onelenyk/agentlight/firmware/src/api.cpp

// Веб-сервер: сторінка лампи і REST. Опис запитів — у docs/firmware.md.
#include <WiFi.h>
#include "app.h"
#include <uri/UriBraces.h>
#include "assets.h"

WebServer server(80);

void sendJson(int code, const JsonDocument& doc) {
  String out;
  serializeJson(doc, out);
  server.send(code, "application/json", out);
}

static void sendError(int code, const char* text) {
  JsonDocument doc;
  doc["error"] = text;
  sendJson(code, doc);
}

static void restartSoon() {
  server.send(200, "application/json", "{\"ok\":true}");
  delay(500);
  ESP.restart();
}

void fillStatus(JsonObject o) {
  o["state"] = STATE_NAMES[aggregate()];
  fillAgents(o["agents"].to<JsonArray>());
  o["brightness"] = brightness;
  o["mode"] = MODE_NAMES[cfg.mode];
  o["off"] = lightOff;
  o["lamp_left"] = lampSecondsLeft();
  o["sleep_left"] = sleepSecondsLeft();
  fillFocus(o["focus"].to<JsonObject>());
  fillGame(o["play"].to<JsonObject>());
  fillAllow(o["allow"].to<JsonObject>());
  fillRemote(o["remote"].to<JsonObject>());          // пульт: спаровані пристрої і хто з них активний
  JsonObject sig = o["signal"].to<JsonObject>();     // дія сенсора «сигнал агентові»
  sig["count"] = signalCount;
  if (signalCount) sig["ago"] = (millis() - signalAt) / 1000;
  fillWifi(o["wifi"].to<JsonObject>());
}

static const char* resetReason() {
  switch (esp_reset_reason()) {
    case ESP_RST_POWERON:  return "увімкнення живлення";
    case ESP_RST_SW:       return "програмний перезапуск";
    case ESP_RST_PANIC:    return "збій прошивки";
    case ESP_RST_INT_WDT:
    case ESP_RST_TASK_WDT:
    case ESP_RST_WDT:      return "сторожовий таймер";
    case ESP_RST_BROWNOUT: return "просідання живлення";
    default:               return "інше";
  }
}

static String hexColor(uint32_t c) {
  char hex[8];
  snprintf(hex, sizeof hex, "#%06x", (unsigned)(c & 0xFFFFFF));
  return hex;
}

static bool parseColor(const char* hex, uint32_t& out) {
  if (strlen(hex) != 7 || hex[0] != '#') return false;
  out = strtoul(hex + 1, nullptr, 16);
  return true;
}

static void fillDebug(JsonObject o) {
  JsonObject d = o["device"].to<JsonObject>();
  d["version"] = FW_VERSION;
  d["build"] = __DATE__ " " __TIME__;
  d["uptime"] = millis() / 1000;
  d["reset"] = resetReason();
  d["chip"] = ESP.getChipModel();
  d["mac"] = WiFi.macAddress();
  d["heap"] = ESP.getFreeHeap();
  d["heap_min"] = ESP.getMinFreeHeap();
  d["led_pin"] = LED_PIN;
  d["led_max"] = LED_COUNT;
  d["touch_pin"] = TOUCH_PIN;
  d["ota_ready"] = otaReady();
  JsonObject t = o["touch"].to<JsonObject>();
  t["raw"] = touchRaw;
  t["count"] = touchCount;
  if (touchCount) t["ago"] = (millis() - touchAt) / 1000;
  JsonObject c = o["settings"].to<JsonObject>();
  c["brightness"] = brightness;
  c["leds"] = cfg.leds;
  c["ttl_busy"] = cfg.ttlBusyMin;
  c["ttl_done"] = cfg.ttlDoneMin;
  c["ttl_attention"] = cfg.ttlAttentionMin;
  for (int8_t i = ST_IDLE; i < ST_COUNT; i++) c["colors"][STATE_NAMES[i]] = hexColor(cfg.color[i]);
  for (int8_t i = ST_IDLE; i < ST_COUNT; i++) c["anims"][STATE_NAMES[i]] = ANIM_NAMES[cfg.anim[i]];
  JsonObject lamp = c["lamp"].to<JsonObject>();
  lamp["color"] = hexColor(cfg.lampColor);
  lamp["anim"] = ANIM_NAMES[cfg.lampAnim];
  lamp["off_min"] = cfg.lampOffMin;
  c["sleep_min"] = cfg.sleepMin;
  JsonObject fc = c["focus"].to<JsonObject>();
  fc["work_min"] = cfg.focusWorkMin;
  fc["break_min"] = cfg.focusBreakMin;
  fc["quiet"] = (bool)cfg.focusQuiet;
  c["webhook"] = webhookUrl;
  for (uint8_t m = 0; m < MODE_COUNT; m++) {
    for (uint8_t g = 0; g < G_COUNT; g++)
      c["touch"][MODE_NAMES[m]][GESTURE_NAMES[g]] = ACTION_NAMES[touchAction((Mode)m, (Gesture)g)];
    JsonArray acts = o["actions"][MODE_NAMES[m]].to<JsonArray>();   // дії, доступні в цьому режимі
    for (uint8_t a = 0; a < ACT_COUNT; a++) if (actionFits(a, (Mode)m)) acts.add(ACTION_NAMES[a]);
  }
  JsonArray anims = o["animations"].to<JsonArray>();
  for (const char* n : ANIM_NAMES) anims.add(n);
}

static void handleStatusGet() {
  JsonDocument doc;
  fillStatus(doc.to<JsonObject>());
  sendJson(200, doc);
}

// Приймає JSON-тіло або параметри запиту: curl -X POST 'http://agentlight.local/api/status?state=busy'
static void handleStatusPost() {
  JsonDocument in;
  String body = server.arg("plain");
  if (body.startsWith("{")) {
    if (deserializeJson(in, body)) return sendError(400, "bad json");
  } else {
    for (const char* key : {"state", "agent_id", "name", "task", "message"})
      if (server.hasArg(key)) in[key] = server.arg(key);
  }
  if (const char* err = applyStatus(in)) return sendError(400, err);
  handleStatusGet();
}

static void handleDebug() {
  JsonDocument doc;
  fillStatus(doc.to<JsonObject>());
  fillDebug(doc.as<JsonObject>());
  sendJson(200, doc);
}

// Індекс назви у списку або fallback, якщо такої немає
static uint8_t indexOf(const char* name, const char* const* names, uint8_t count, uint8_t fallback) {
  for (uint8_t i = 0; i < count; i++)
    if (!strcmp(name, names[i])) return i;
  return fallback;
}

// Приймає будь-яку підмножину налаштувань; чого не передали — лишається як було
static void handleConfig() {
  JsonDocument in;
  if (deserializeJson(in, server.arg("plain"))) return sendError(400, "bad json");
  setBrightness(in["brightness"] | (int)brightness);
  cfg.leds = constrain(in["leds"] | (int)cfg.leds, 1, LED_COUNT);
  cfg.ttlBusyMin = constrain(in["ttl_busy"] | (int)cfg.ttlBusyMin, 0, 1440);
  cfg.ttlDoneMin = constrain(in["ttl_done"] | (int)cfg.ttlDoneMin, 0, 1440);
  cfg.ttlAttentionMin = constrain(in["ttl_attention"] | (int)cfg.ttlAttentionMin, 0, 1440);
  for (int8_t i = ST_IDLE; i < ST_COUNT; i++) {
    parseColor(in["colors"][STATE_NAMES[i]] | "", cfg.color[i]);
    cfg.anim[i] = indexOf(in["anims"][STATE_NAMES[i]] | "", ANIM_NAMES, AN_COUNT, cfg.anim[i]);
  }
  if (in["lamp"].is<JsonObjectConst>()) {
    parseColor(in["lamp"]["color"] | "", cfg.lampColor);
    cfg.lampAnim = indexOf(in["lamp"]["anim"] | "", ANIM_NAMES, AN_COUNT, cfg.lampAnim);
    cfg.lampOffMin = constrain(in["lamp"]["off_min"] | (int)cfg.lampOffMin, 0, 1440);
    lightSwitch(true);                  // зміну видно одразу, таймер рахує заново
  }
  if (in["remote"]["active"].is<const char*>()) remoteSetActive(in["remote"]["active"].as<String>());
  for (JsonPairConst name : in["remote"]["names"].as<JsonObjectConst>()) remoteSetName(name.key().c_str(), name.value() | "");
  if (in["allow"].is<JsonObjectConst>()) {
    JsonObjectConst a = in["allow"];
    cfg.allowEnabled = a["enabled"] | (bool)cfg.allowEnabled;
    cfg.allowCats = ((a["edits"] | (bool)(cfg.allowCats & 1)) ? 1 : 0) | ((a["commands"] | (bool)(cfg.allowCats & 2)) ? 2 : 0)
                  | ((a["other"] | (bool)(cfg.allowCats & 4)) ? 4 : 0);
  }
  cfg.diceKind = constrain(in["dice"] | (int)cfg.diceKind, 0, Games::DICE_COUNT - 1);
  if (in["game"].is<int>()) {
    cfg.gameSel = constrain(in["game"].as<int>(), 0, Games::GAME_COUNT - 1);
    games.select(cfg.gameSel, millis());
  }
  cfg.sleepMin = constrain(in["sleep_min"] | (int)cfg.sleepMin, 1, 240);
  cfg.focusWorkMin = constrain(in["focus"]["work_min"] | (int)cfg.focusWorkMin, 1, 180);
  cfg.focusBreakMin = constrain(in["focus"]["break_min"] | (int)cfg.focusBreakMin, 1, 60);
  cfg.focusQuiet = in["focus"]["quiet"] | (bool)cfg.focusQuiet;
  if (in["webhook"].is<const char*>()) setWebhook(in["webhook"].as<String>());
  for (uint8_t m = 0; m < MODE_COUNT; m++)
    for (uint8_t g = 0; g < G_COUNT; g++) {
      uint8_t& slot = touchAction((Mode)m, (Gesture)g);
      uint8_t  want = indexOf(in["touch"][MODE_NAMES[m]][GESTURE_NAMES[g]] | "", ACTION_NAMES, ACT_COUNT, slot);
      if (actionFits(want, (Mode)m)) slot = want;
    }
  saveSettings();
  uint8_t mode = indexOf(in["mode"] | "", MODE_NAMES, MODE_COUNT, cfg.mode);
  if (mode != cfg.mode) setMode((Mode)mode);
  handleDebug();
}

// Разові дії зі сторінки
static void handleAction() {
  JsonDocument in;
  deserializeJson(in, server.arg("plain"));
  String action = in["action"] | "";
  if (action == "reboot") return restartSoon();
  if (action == "rainbow") startRainbow(10000);
  else if (action == "preview") {   // {"action":"preview","state":"waiting"}: 6 с показує вигляд цього стану
    uint8_t st = indexOf(in["state"] | "", STATE_NAMES, ST_COUNT, ST_COUNT);
    if (st == ST_COUNT) return sendError(400, "unknown state");
    startPreview((State)st, 6000);
  }
  else if (action == "clear") clearAgents(false);
  else if (action == "on") lightSwitch(true);
  else if (action == "off") lightSwitch(false);
  else if (action == "toggle") lightSwitch(lightOff);
  else if (action == "game_tap") { games.press(millis()); games.release(millis()); }   // дотик у грі зі сторінки
  else if (action == "game_records") resetRecords();
  else if (action == "remote_forget") remoteForget(in["id"] | "");
  // macOS, уперше побачивши клавіатуру, просить натиснути клавіші біля лівого й правого Shift, щоб визначити
  // розкладку. У лампи клавіш немає, тож ці дві натискаються зі сторінки. Інших клавіш звідси надіслати не можна.
  else if (action == "remote_key_left") remoteKey(0x1D);    // Z
  else if (action == "remote_key_right") remoteKey(0x38);   // /
  else if (indexOf(action.c_str(), ACTION_NAMES, ACT_COUNT, ACT_COUNT) != ACT_COUNT) {   // будь-яка дія сенсора, зі сторінки
    uint8_t act = indexOf(action.c_str(), ACTION_NAMES, ACT_COUNT, ACT_COUNT);
    if (!actionFits(act, (Mode)cfg.mode)) return sendError(400, "action does not fit this mode");
    runAction(act);
  }
  else if (action == "defaults") { cfg = Settings(); saveSettings(); }
  else return sendError(400, "unknown action");
  handleDebug();
}

static void handleScan() {
  Net found[20];
  size_t count = scanNets(found, 20);
  JsonDocument doc;
  JsonArray list = doc.to<JsonArray>();
  for (size_t i = 0; i < count; i++) {
    JsonObject o = list.add<JsonObject>();
    o["ssid"] = found[i].ssid;
    o["rssi"] = found[i].rssi;
  }
  sendJson(200, doc);
}

static void handleWifiSave() {
  JsonDocument in;
  if (deserializeJson(in, server.arg("plain")) || !strlen(in["ssid"] | "")) return sendError(400, "ssid required");
  addNet(in["ssid"] | "", in["pass"] | "");
  restartSoon();
}

// Забуває одну мережу (ssid у тілі) або всі
static void handleWifiReset() {
  JsonDocument in;
  deserializeJson(in, server.arg("plain"));
  forgetNet(in["ssid"] | "");
  restartSoon();
}

void apiBegin() {
  server.on("/", HTTP_GET, [] {
    server.sendHeader("Content-Encoding", "gzip");
    server.send_P(200, "text/html", (const char*)PAGE_GZ, PAGE_GZ_LEN);
  });
  // Усе, щоб підключити агента без жодних файлів на руках: встановлювач і готові хуки
  server.on("/install.sh", HTTP_GET, [] {
    String script = "LAMP='http://" + WiFi.localIP().toString() + "'\n";
    script.concat((const char*)INSTALL_SH, INSTALL_SH_LEN);
    server.send(200, "text/plain; charset=utf-8", script);
  });
  server.on(UriBraces("/setup/{}"), HTTP_GET, [] {
    for (auto& f : SETUP_FILES) {
      if (server.pathArg(0) != f.name) continue;
      server.sendHeader("Content-Encoding", "gzip");
      return server.send_P(200, f.type, (const char*)f.data, f.len);
    }
    server.send(404, "text/plain", "Not found");
  });
  server.on("/api/status", HTTP_GET, handleStatusGet);
  server.on("/api/status", HTTP_POST, handleStatusPost);
  server.on("/api/config", HTTP_POST, handleConfig);
  server.on("/api/debug", HTTP_GET, handleDebug);
  server.on("/api/action", HTTP_POST, handleAction);
  server.on("/api/scan", HTTP_GET, handleScan);
  server.on("/api/wifi", HTTP_POST, handleWifiSave);
  server.on("/api/wifi/reset", HTTP_POST, handleWifiReset);
  server.on("/mcp", HTTP_POST, handleMcp);
  server.on("/mcp", HTTP_GET, [] { server.send(405, "text/plain", "Method Not Allowed"); });  // SSE-потоку немає
  server.onNotFound([] {
    if (!portal) return server.send(404, "text/plain", "Not found");
    server.sendHeader("Location", "http://" + WiFi.softAPIP().toString() + "/");   // портал: будь-яка адреса веде на сторінку
    server.send(302, "text/plain", "");
  });
  otaBegin();
  hookBegin();
  allowBegin();
  server.begin();
}
