onelenyk/agentlight/firmware/src/light.cpp

// Діоди: один ланцюжок WS2812 на LED_PIN. У режимі агентів колір і анімація залежать від стану WiFi й агентів,
// у режимі лампи — від налаштувань лампи.
#include <Adafruit_NeoPixel.h>
#include <WiFi.h>
#include "app.h"

static Adafruit_NeoPixel strip(LED_COUNT, LED_PIN, NEO_GRB + NEO_KHZ800);
static uint32_t rainbowUntil = 0, flashUntil = 0, previewUntil = 0;
static State    previewState = ST_IDLE;
bool lightOff = false;
static uint32_t onAt = 0;       // коли світло ввімкнули: від цього моменту рахує таймер режиму лампи
static uint32_t sleepAt = 0;    // коли запустили таймер сну; 0 — не запущений
static int8_t   pickMode = -1;  // режим, колір якого показуємо під час вибору утриманням

const uint32_t FOCUS_WORK = 0xFF2D55, FOCUS_BREAK = 0x00D08A;

const uint8_t FLASH_MIN = 90;   // спалах на дотик видно й на найтьмянішій яскравості

void lightBegin() { strip.begin(); }

void lightSwitch(bool on) {
  lightOff = !on;
  onAt = millis();
  sleepAt = 0;                  // будь-яке перемикання світла скасовує таймер сну
}

void lightPick(int8_t mode) { pickMode = mode; }

void startSleep() {
  lightOff = false;
  sleepAt = millis() ? millis() : 1;
}

uint32_t sleepSecondsLeft() {
  if (!sleepAt || lightOff) return 0;
  uint32_t total = cfg.sleepMin * 60UL, passed = (millis() - sleepAt) / 1000;
  return passed < total ? total - passed : 0;
}

uint32_t lampSecondsLeft() {
  if (cfg.mode != MODE_LAMP || lightOff || !cfg.lampOffMin) return 0;
  uint32_t total = cfg.lampOffMin * 60UL, passed = (millis() - onAt) / 1000;
  return passed < total ? total - passed : 0;
}
void startRainbow(uint32_t ms) { rainbowUntil = millis() + ms; }
void flash(uint16_t ms) { flashUntil = millis() + ms; }
void startPreview(State st, uint32_t ms) { previewState = st; previewUntil = millis() + ms; }

static void show(uint8_t level = brightness) {
  strip.setBrightness(level);
  strip.show();
}

static void fill(uint32_t rgb, float k, uint8_t level = brightness) {
  strip.clear();
  strip.fill(Adafruit_NeoPixel::Color((rgb >> 16 & 255) * k, (rgb >> 8 & 255) * k, (rgb & 255) * k), 0, cfg.leds);
  show(level);
}

void lightSolid(uint32_t rgb) { fill(rgb, 0.5f); }

static float triangle(float x) { return x < 0 || x > 1 ? 0 : 1 - fabsf(2 * x - 1); }   // 0 → 1 → 0 на відрізку [0, 1]

// Яскравість діода i з n у момент t (мс), від 0 до 1. Діоди стоять по колу, тому «по колу» — це по індексу.
static float animLevel(uint8_t anim, uint32_t t, uint8_t i, uint8_t n) {
  static float spark[LED_COUNT];
  const float dim = 0.06f;
  switch (anim) {
    case AN_BREATHE:   return 0.3f + 0.7f * (0.5f + 0.5f * sinf(t / 1000.0f * PI));          // період 2 с
    case AN_BLINK:     return (t / 500) % 2 ? 1.0f : 0.08f;
    case AN_SPIN:      return (t / 250) % n == i ? 1.0f : dim;                               // один вогник біжить по колу
    case AN_COMET: {                                                                         // голова з хвостом, плавно
      float behind = fmodf(fmodf(t / 300.0f, n) - i + n, n) / n;
      return max(dim, (1 - behind) * (1 - behind) * (1 - behind));
    }
    case AN_WAVE:      return 0.12f + 0.88f * (0.5f + 0.5f * sinf(t / 1000.0f * 1.4f * PI - i * 2 * PI / n));
    case AN_HEARTBEAT: {                                                                     // два удари і пауза
      float ms = t % 1200;
      return 0.1f + 0.9f * max(triangle(ms / 180.0f), 0.7f * triangle((ms - 260) / 200.0f));
    }
    case AN_SPARKLE:                                                                         // випадкові спалахи, що згасають
      if (esp_random() % 100 < 6) spark[i] = 1; else spark[i] *= 0.88f;
      return 0.1f + 0.9f * spark[i];
    case AN_PENDULUM: {                                                                      // туди й назад
      uint8_t steps = n > 1 ? 2 * n - 2 : 1, step = (t / 220) % steps;
      return (step < n ? step : steps - step) == i ? 1.0f : dim;
    }
    case AN_FILL:      return i < (t / 350) % (n + 2) ? 1.0f : dim;                          // загоряються по одному, потім усі гаснуть
    case AN_BEACON: {                                                                        // два короткі спалахи і пауза
      uint16_t ms = t % 1400;
      return ms < 90 || (ms >= 180 && ms < 270) ? 1.0f : 0.05f;
    }
    default:           return 1.0f;
  }
}

static void showLook(uint32_t rgb, uint8_t anim, uint32_t t) {
  strip.clear();
  for (uint8_t i = 0; i < cfg.leds; i++) {
    if (anim == AN_RAINBOW) {             // кольори по колу, власний колір не використовується
      strip.setPixelColor(i, Adafruit_NeoPixel::gamma32(Adafruit_NeoPixel::ColorHSV(t * 8 + i * 65536UL / cfg.leds)));
      continue;
    }
    float k = animLevel(anim, t, i, cfg.leds);
    strip.setPixelColor(i, (uint8_t)((rgb >> 16 & 255) * k), (uint8_t)((rgb >> 8 & 255) * k), (uint8_t)((rgb & 255) * k));
  }
  show();
}

static void showState(State st, uint32_t t) { showLook(cfg.color[st], cfg.anim[st], t); }

// Режим фокусу: діоди — це шкала часу, що лишився. Гаснуть по одному, поточний тьмяніє.
static void showFocus(uint32_t t, float breathe) {
  uint32_t rgb = focus.phase == Focus::BREAK ? FOCUS_BREAK : FOCUS_WORK;
  State agents = aggregate();
  bool attention = agents >= ST_WAITING && !(cfg.focusQuiet && focus.phase == Focus::WORK);
  if (attention && (t / 250) % 12 == 0) return fill(cfg.color[agents], 1.0f);      // раз на 3 с: агент чекає
  if (focus.phase == Focus::IDLE) return fill(rgb, 0.12f + 0.1f * breathe);         // готовий, чекає дотику
  if (focus.alerting(t)) return fill(rgb, (t / 250) % 2 ? 1.0f : 0.05f);            // відрізок змінився
  float lit = focus.totalMs ? (float)focus.leftMs / focus.totalMs * cfg.leds : 0;
  strip.clear();
  for (uint8_t i = 0; i < cfg.leds; i++) {
    float k = constrain(lit - i, 0.03f, 1.0f) * (focus.paused ? breathe : 1.0f);
    strip.setPixelColor(i, (uint8_t)((rgb >> 16 & 255) * k), (uint8_t)((rgb >> 8 & 255) * k), (uint8_t)((rgb & 255) * k));
  }
  show();
}

void render() {
  static uint32_t last = 0;
  if (millis() - last < FRAME_MS) return;
  last = millis();
  float breathe = 0.3f + 0.7f * (0.5f + 0.5f * sinf(last / 1000.0f * PI));  // період 2 с
  if (last < flashUntil) return fill(0xFFFFFF, 1.0f, max(brightness, FLASH_MIN));  // спалах: дотик почуто
  if (pickMode >= 0) return fill(MODE_COLORS[pickMode], 1.0f, max(brightness, FLASH_MIN));   // вибір режиму утриманням
  if (allowAsking()) return showLook(0xFFB000, AN_COMET, last * 2);      // агент просить дозвіл: бурштинова комета
  if (allowPairing()) return fill(0x00C8FF, (last / 200) % 2 ? 1.0f : 0.1f);   // комп'ютер просить спаруватись
  if (last < rainbowUntil) return showLook(0, AN_RAINBOW, last);         // тест діодів зі сторінки
  if (last < previewUntil) return showState(previewState, last);         // проба анімації зі сторінки
  if (cfg.mode == MODE_LAMP) {                                           // просто лампа: стан WiFi й агентів не показуємо
    if (!lightOff && cfg.lampOffMin && millis() - onAt > cfg.lampOffMin * 60000UL) lightOff = true;
    uint8_t wanted = brightness;
    if (sleepAt && !lightOff) {                                          // таймер сну: яскравість плавно сходить до нуля
      float left = 1.0f - (float)(millis() - sleepAt) / (cfg.sleepMin * 60000.0f);
      if (left <= 0) { lightOff = true; sleepAt = 0; }
      else brightness = max(1, (int)(wanted * left));
    }
    if (lightOff) return fill(0, 0);
    showLook(cfg.lampColor, cfg.lampAnim, last);
    brightness = wanted;
    return;
  }
  if (cfg.mode == MODE_MUSIC) {                                          // пульт: хвиля, коли є кому слати клавіші
    if (lightOff) return fill(0, 0);
    if (remoteConnected()) return showLook(MODE_COLORS[MODE_MUSIC], AN_WAVE, last);
    return fill(MODE_COLORS[MODE_MUSIC], (last / 700) % 2 ? 0.35f : 0.05f);   // блимає: ніхто не підключений
  }
  if (cfg.mode == MODE_GAMES) {
    if (lightOff) return fill(0, 0);
    State agents = aggregate();                                          // між раундами нагадуємо, що агент чекає
    if (games.idle() && agents >= ST_WAITING && (last / 250) % 12 == 0) return fill(cfg.color[agents], 1.0f);
    uint32_t frame[LED_COUNT] = {};
    games.render(last, frame);
    strip.clear();
    for (uint8_t i = 0; i < cfg.leds; i++) strip.setPixelColor(i, frame[i]);
    return show();
  }
  if (cfg.mode == MODE_FOCUS) {
    if (lightOff) return fill(0, 0);                                     // таймер іде далі й без світла
    return showFocus(last, breathe);
  }
  if (portal) return fill(0x003CFF, breathe);                            // синій: режим налаштування
  if (WiFi.status() != WL_CONNECTED) return fill(0x9600FF, breathe);     // фіолетовий: немає WiFi
  State st = aggregate();
  if (lightOff) return fill(0, 0);
  showState(st, last);                                                   // спокій типово чорний, тобто темно
}
