onelenyk/agentlight/tests/e2e_lamp.py

"""Наскрізна перевірка справжньої лампи: усе, що можна перевірити без пальця на сенсорі й без очей.

  python3 tests/e2e_lamp.py --lamp 192.168.1.50 [--only hooks,ota] [--json звіт.json]

Лампа має бути в тій самій мережі. Перевірка змінює її налаштування, кілька разів перезавантажує й оновлює,
а наприкінці повертає все як було. Триває близько 12 хвилин.

Що потрібно на комп'ютері: curl, openssl, компілятор C++, node і npm (для справжніх CLI агентів).
Необов'язково: bleak (перевірки Bluetooth), ключ підпису прошивки й PlatformIO (перевірки оновлення).
Розділ allow повний лише на збірці з прапорцем ALLOW_TEST_TOUCH: у звичайній «торкнутись» лампи запитом не можна.
"""
import argparse
import base64
import gzip
import hashlib
import hmac
import json
import os
import pathlib
import shutil
import subprocess
import sys
import tempfile
import threading
import time
import urllib.error
import urllib.request

sys.path.insert(0, str(pathlib.Path(__file__).resolve().parent))
import mock_model  # noqa: E402
from mock_lamp import parse_hook  # noqa: E402

ROOT = pathlib.Path(__file__).resolve().parent.parent
HOOKS = ROOT / "hooks"
FIRMWARE = ROOT / "firmware"
KEY = pathlib.Path.home() / ".config" / "agentlight" / "firmware-signing-key.pem"
PAGES = "https://onelenyk.github.io/agentlight/"
results = []          # (розділ, перевірка, "ok" | "FAIL" | "skip", подробиці)
section = ""


class Skip(Exception):
    pass


def check(name):
    """Декоратор: запускає перевірку одразу й записує результат; текст із return іде в подробиці."""
    def run(fn):
        try:
            detail = fn() or ""
            results.append((section, name, "ok", detail))
        except Skip as why:
            results.append((section, name, "skip", str(why)))
        except Exception as error:  # noqa: BLE001 — будь-яка помилка є результатом перевірки
            results.append((section, name, "FAIL", f"{type(error).__name__}: {error}"[:400]))
        mark = {"ok": "  ok  ", "FAIL": " FAIL ", "skip": " skip "}[results[-1][2]]
        print(f"[{mark}] {section}: {name}" + (f" — {results[-1][3]}" if results[-1][3] else ""), flush=True)
        return fn
    return run


def call(path, body=None, method=None, headers=None, raw=False, timeout=10):
    data = body if isinstance(body, bytes) else json.dumps(body).encode() if body is not None else None
    request = urllib.request.Request(LAMP + path, data=data, method=method or ("POST" if data is not None else "GET"),
                                     headers={"Content-Type": "application/json", **(headers or {})})
    try:
        with urllib.request.urlopen(request, timeout=timeout) as response:
            code, content = response.status, response.read()
    except urllib.error.HTTPError as error:
        code, content = error.code, error.read()
    return (code, content) if raw else json.loads(content or b"{}")


def status():
    return call("/api/status")


def debug():
    return call("/api/debug")


def config(patch):
    return call("/api/config", patch)


def action(name, **extra):
    return call("/api/action", {"action": name, **extra})


def agent(agent_id):
    return next((a for a in status()["agents"] if a["id"] == agent_id), None)


def wait_online(seconds=40):
    deadline = time.time() + seconds
    while time.time() < deadline:
        try:
            if not status()["wifi"]["portal"]:
                return
        except Exception:  # noqa: BLE001
            pass
        time.sleep(1)
    raise AssertionError("лампа не повернулась у мережу")


def sh(command, env=None, timeout=120, stdin=None):
    return subprocess.run(command, shell=True, env=env, capture_output=True, text=True, timeout=timeout, input=stdin)


def watch(prefix, seconds, stop, name="project-e2e"):
    """Збирає послідовність (стан, повідомлення) агента з таким початком id і назвою проєкту, поки триває перевірка.
    Назва потрібна, бо на лампі можуть бути й справжні сесії того самого агента."""
    seen = []

    def loop():
        deadline = time.time() + seconds
        while time.time() < deadline and not stop.is_set():
            try:
                now = [(a["state"], a["message"]) for a in status()["agents"] if a["id"].startswith(prefix) and a["name"] == name]
            except Exception:  # noqa: BLE001
                now = None
            if now is not None:
                value = now[0] if now else ("gone", "")
                if not seen or seen[-1] != value:
                    seen.append(value)
            time.sleep(0.25)
    thread = threading.Thread(target=loop, daemon=True)
    thread.start()
    return seen, thread


def clear_agents(prefix, name="project-e2e"):
    for a in status()["agents"]:
        if a["id"].startswith(prefix) and a["name"] in (name, "e2e-hook", "project"):
            call(f"/api/status?state=idle&agent_id={a['id']}", b"")


parser = argparse.ArgumentParser(description=__doc__.split("\n")[0])
parser.add_argument("--lamp", required=True, help="адреса лампи, наприклад 192.168.1.50")
parser.add_argument("--only", default="", help="розділи через кому; без цього — всі")
parser.add_argument("--json", type=pathlib.Path, help="куди записати результати")
args = parser.parse_args()
LAMP = "http://" + args.lamp
only = set(filter(None, args.only.split(",")))
wanted = lambda name: not only or name in only  # noqa: E731
saved = debug()["settings"]
saved_mode = status()["mode"]
work = pathlib.Path(tempfile.mkdtemp(prefix="agentlight-e2e-"))

# ------------------------------------------------------------------------------------------------ основа
if wanted("base"):
    section = "Основа"

    @check("лампа відповідає й каже, хто вона")
    def _():
        d = debug()
        assert d["device"]["chip"] == "ESP32-C3" and d["wifi"]["ip"] == args.lamp
        return f"версія {d['device']['version']}, зібрана {d['device']['build']}, вільно {d['device']['heap'] // 1024} КБ"

    @check("ім'я agentlight.local веде на цю лампу")
    def _():
        out = sh("curl -4 -s -m 8 http://agentlight.local/api/status").stdout
        assert json.loads(out)["wifi"]["ip"] == args.lamp

    @check("сторінка віддається стиснутою й містить усі режими")
    def _():
        code, body = call("/", raw=True)
        page = gzip.decompress(body).decode() if body[:2] == b"\x1f\x8b" else body.decode()
        for part in ('id="p_agents"', 'id="p_lamp"', 'id="p_focus"', 'id="p_games"', 'id="p_music"', 'id="al_on"', 'id="updbtn"'):
            assert part in page, part
        assert page == (FIRMWARE / "src" / "page.html").read_text(encoding="utf-8"), "сторінка на лампі не та, що в репозиторії"
        return f"{len(body) / 1024:.1f} КБ у мережі, {len(page) / 1024:.0f} КБ розгорнута"

    @check("невідома адреса дає 404")
    def _():
        assert call("/nope", raw=True)[0] == 404

# ------------------------------------------------------------------------------------------------ агенти
if wanted("agents"):
    section = "Агенти"
    config({"mode": "agents"})
    action("clear")

    @check("стан приймається тілом JSON і параметрами запиту")
    def _():
        call("/api/status", {"state": "busy", "agent_id": "e2e-a", "name": "проєкт", "task": "завдання", "message": "крок 1"})
        a = agent("e2e-a")
        assert (a["state"], a["name"], a["task"], a["message"]) == ("busy", "проєкт", "завдання", "крок 1")
        call("/api/status?state=done&agent_id=e2e-b&name=other", b"")
        assert agent("e2e-b")["state"] == "done"

    @check("назва й завдання зберігаються, повідомлення — ні")
    def _():
        call("/api/status", {"state": "busy", "agent_id": "e2e-a"})
        a = agent("e2e-a")
        assert (a["name"], a["task"], a["message"]) == ("проєкт", "завдання", "")

    @check("лампа показує найважливіший стан")
    def _():
        order = []
        for state in ("done", "busy", "waiting", "error"):
            call("/api/status", {"state": state, "agent_id": "e2e-" + state})
            order.append(status()["state"])
        assert order == ["busy", "busy", "waiting", "error"], order   # e2e-a вже busy, тож done його не перекриває
        call("/api/status", {"state": "idle", "agent_id": "e2e-error"})
        assert status()["state"] == "waiting"
        return "готово < працює < чекає < помилка"

    @check("idle прибирає агента; невідомий стан відхиляється")
    def _():
        call("/api/status", {"state": "idle", "agent_id": "e2e-b"})
        assert agent("e2e-b") is None
        assert call("/api/status", {"state": "sleeping"}, raw=True)[0] == 400

    @check("більше восьми агентів: найстаріший витісняється")
    def _():
        action("clear")
        for i in range(9):
            call("/api/status", {"state": "busy", "agent_id": f"e2e-slot{i}"})
            time.sleep(0.15)
        ids = {a["id"] for a in status()["agents"]}
        assert len(ids) == 8 and "e2e-slot0" not in ids and "e2e-slot8" in ids, ids

    @check("довгий текст обрізається без поламаних літер")
    def _():
        call("/api/status", {"state": "busy", "agent_id": "e2e-long", "name": "я" * 100, "task": "щ" * 500, "message": "ї" * 300})
        a = agent("e2e-long")
        assert len(a["name"].encode()) <= 44 and len(a["task"].encode()) <= 244 and a["name"].endswith("…")
        a["name"].encode().decode()

    @check("«прибрати всіх» очищає список")
    def _():
        action("clear")
        assert status()["agents"] == [] and status()["state"] == "idle"

# ------------------------------------------------------------------------------------------------ хуки
if wanted("hooks"):
    section = "Хуки агентів"

    @check("усі зразки подій лампа розбирає так само, як тести")
    def _():
        cases = json.loads((ROOT / "tests" / "hook_cases.json").read_text(encoding="utf-8"))
        bad = []
        for i, case in enumerate(cases):
            body = (case["raw"] if "raw" in case else json.dumps(case["body"], ensure_ascii=False)).replace("REPEAT_X_9000", "x" * 9000).encode()
            body = body[:case.get("truncate", len(body))]
            want = parse_hook(case["tool"], case["state"], body)
            action("clear")
            call(f"/hook/{case['tool']}/{case['state']}", body)
            agents = status()["agents"]
            if want.get("skip") or want["state"] == "idle":
                if agents:
                    bad.append(case["name"])
                continue
            got = agents[0] if agents else {}
            if any(got.get(k) != want[v] for k, v in (("id", "agent_id"), ("state", "state"), ("name", "name"), ("message", "message"), ("task", "task"))):
                bad.append(f"{case['name']}: {got}")
        action("clear")
        assert not bad, bad
        return f"{len(cases)} зразків від семи агентів"

    @check("лампа роздає ті самі файли хуків, що в репозиторії")
    def _():
        names = sorted(p.name for p in HOOKS.iterdir() if p.suffix in (".json", ".js", ".sh") and p.name != "install.sh")
        for name in names:
            code, body = call("/setup/" + name, raw=True)
            assert code == 200 and gzip.decompress(body) == (HOOKS / name).read_bytes(), name
        code, script = call("/install.sh", raw=True)
        assert script.decode().split("\n", 1) == [f"LAMP='{LAMP}'", (HOOKS / "install.sh").read_text(encoding="utf-8")]
        return f"{len(names)} файлів і встановлювач"

    @check("встановлювач із лампи ставить хуки всім восьми агентам")
    def _():
        home = work / "install-home"
        home.mkdir()
        targets = {"claude": ".claude/settings.json", "codex": ".codex/hooks.json", "gemini": ".gemini/settings.json",
                   "qwen": ".qwen/settings.json", "cursor": ".cursor/hooks.json", "antigravity": ".gemini/config/hooks.json",
                   "copilot": ".copilot/hooks/agentlight.json", "opencode": ".config/opencode/plugins/agentlight.js"}
        for name, target in targets.items():
            result = sh(f"curl -4 -fsS {LAMP}/install.sh | sh -s -- {name}", env=dict(os.environ, HOME=str(home)))
            assert result.returncode == 0 and (home / target).stat().st_size > 100, f"{name}: {result.stderr}"
        return ", ".join(targets)

    @check("встановлений хук Claude Code доходить до лампи за її іменем")
    def _():
        hooks = json.loads((work / "install-home" / ".claude" / "settings.json").read_text())["hooks"]
        event = {"session_id": "e2ehook1-x", "cwd": "/tmp/e2e-hook", "hook_event_name": "UserPromptSubmit", "prompt": "перевірка"}
        sh(hooks["UserPromptSubmit"][0]["hooks"][0]["command"], stdin=json.dumps(event))
        time.sleep(1.5)
        a = agent("claude-e2ehook1")
        assert a and (a["state"], a["name"], a["task"]) == ("busy", "e2e-hook", "перевірка"), a
        clear_agents("claude-e2ehook1")

# ------------------------------------------------------------------------------------------------ справжні CLI
if wanted("cli"):
    section = "Справжні програми агентів"
    tools = work / "cli"
    installed = sh(f"npm install --prefix {tools} --no-audit --no-fund @anthropic-ai/claude-code @openai/codex @qwen-code/qwen-code", timeout=400)
    bin_dir = tools / "node_modules" / ".bin"

    def version(program):
        return sh(f"{bin_dir / program} --version").stdout.strip().splitlines()[-1]

    def fresh_home(name, agent_name):
        home = work / name
        (home / "project-e2e").mkdir(parents=True)
        env = {"PATH": os.environ["PATH"], "HOME": str(home)}
        result = sh(f"curl -4 -fsS {LAMP}/install.sh | sh -s -- {agent_name}", env=env)
        assert result.returncode == 0, result.stderr
        return home, env

    def claude_turn(prompt, extra=(), tool_input=None):
        home, env = fresh_home("claude-" + hashlib.md5((prompt + str(extra) + str(tool_input)).encode()).hexdigest()[:6], "claude")
        mock_model.TOOL_NAME = "Bash"
        mock_model.TOOL_INPUT = tool_input or {"command": "echo canary", "description": "Print canary"}
        stop = threading.Event()
        seen, thread = watch("claude-", 60, stop)
        with mock_model.MockModel() as model:
            env.update({"CLAUDE_CONFIG_DIR": str(home / ".claude"), "ANTHROPIC_API_KEY": "sk-ant-not-real", "ANTHROPIC_BASE_URL": model.url,
                        "DISABLE_TELEMETRY": "1", "DISABLE_AUTOUPDATER": "1", "CLAUDE_CODE_DISABLE_NONESSENTIAL_TRAFFIC": "1"})
            proc = subprocess.Popen([str(bin_dir / "claude"), "-p", "--input-format", "stream-json", "--output-format", "stream-json",
                                     "--verbose", *extra], cwd=home / "project-e2e", env=env, stdin=subprocess.PIPE,
                                    stdout=subprocess.PIPE, stderr=subprocess.STDOUT, text=True)
            proc.stdin.write(json.dumps({"type": "user", "message": {"role": "user", "content": prompt}}) + "\n")
            proc.stdin.flush()
            deadline = time.time() + 60
            for line in proc.stdout:
                if '"type":"result"' in line or time.time() > deadline:
                    break
            time.sleep(2.5)
            proc.stdin.close()
            try:
                proc.wait(timeout=20)
            except subprocess.TimeoutExpired:
                proc.kill()
            time.sleep(2.5)
        stop.set()
        thread.join()
        clear_agents("claude-")
        return seen[1:] if seen[:1] == [("gone", "")] else seen     # перше «немає» — це ще до початку сесії

    @check("Claude Code: відповідь — працює, готово, спокій")
    def _():
        assert installed.returncode == 0, installed.stderr[-300:]
        seen = claude_turn("reply with ok")
        assert seen == [("busy", "думає"), ("done", ""), ("gone", "")], seen
        return version("claude")

    @check("Claude Code: виклик інструмента показує, що саме робить агент")
    def _():
        seen = claude_turn("USE_TOOL please", ["--dangerously-skip-permissions"])
        assert seen == [("busy", "думає"), ("busy", "Bash: Print canary"), ("done", ""), ("gone", "")], seen

    @check("Claude Code: помилка API дає стан «помилка»")
    def _():
        seen = claude_turn("FAIL please")
        assert [s[0] for s in seen] == ["busy", "error", "gone"] and seen[1][1].startswith("Помилка:"), seen
        return seen[1][1]

    @check("Claude Code: запит дозволу дає стан «чекає» з назвою дії")
    def _():
        seen = claude_turn("USE_TOOL please", ["--permission-mode", "default"], {"command": "touch e2e.txt", "description": "Create a marker file"})
        assert ("waiting", "Дозвіл — Bash: Create a marker file") in seen, seen

    @check("Codex CLI: працює із запитом і проєктом, потім спокій")
    def _():
        home, env = fresh_home("codex", "codex")
        env["CODEX_HOME"] = str(home / ".codex")
        stop = threading.Event()
        seen, thread = watch("codex-", 40, stop)
        details = {}

        def grab():
            for _ in range(60):
                found = [a for a in status()["agents"] if a["id"].startswith("codex-") and a["name"] == "project-e2e"]
                if found:
                    details.update(found[0])
                    return
                time.sleep(0.2)
        grabber = threading.Thread(target=grab, daemon=True)
        grabber.start()
        try:
            subprocess.run([str(bin_dir / "codex"), "exec", "--skip-git-repo-check", "--dangerously-bypass-hook-trust", "reply with ok"],
                           cwd=home / "project-e2e", env=env, stdin=subprocess.DEVNULL, capture_output=True, timeout=60)
        except subprocess.TimeoutExpired:
            pass
        time.sleep(2)
        stop.set()
        thread.join()
        grabber.join()
        clear_agents("codex-")
        assert ("busy", "думає") in seen and seen[-1] == ("gone", ""), seen
        assert (details.get("name"), details.get("task")) == ("project-e2e", "reply with ok"), details
        return version("codex") + "; без входу в акаунт, до відповіді моделі не доходить"

    @check("Qwen Code: працює із запитом і проєктом")
    def _():
        home, env = fresh_home("qwen", "qwen")
        env.update({"OPENAI_API_KEY": "sk-not-real", "OPENAI_BASE_URL": "http://127.0.0.1:9/v1", "OPENAI_MODEL": "none"})
        details = {}

        def grab():
            for _ in range(100):
                found = [a for a in status()["agents"] if a["id"].startswith("qwen-") and a["name"] == "project-e2e"]
                if found:
                    details.update(found[0])
                    return
                time.sleep(0.2)
        grabber = threading.Thread(target=grab, daemon=True)
        grabber.start()
        try:
            subprocess.run([str(bin_dir / "qwen"), "--auth-type", "openai", "-p", "reply with ok"], cwd=home / "project-e2e", env=env,
                           stdin=subprocess.DEVNULL, capture_output=True, timeout=60)
        except subprocess.TimeoutExpired:
            pass
        grabber.join()
        clear_agents("qwen-")
        assert (details.get("state"), details.get("name"), details.get("task")) == ("busy", "project-e2e", "reply with ok"), details
        return version("qwen") + "; без входу в акаунт"

    @check("OpenCode: працює з назвою інструмента, потім готово")
    def _():
        opencode = pathlib.Path.home() / ".opencode" / "bin" / "opencode"
        if not opencode.exists():
            raise Skip("OpenCode не встановлений")
        home, env = fresh_home("opencode", "opencode")
        mock_model.TOOL_NAME = "bash"
        mock_model.TOOL_INPUT = {"command": "echo canary", "description": "Print canary"}
        stop = threading.Event()
        seen, thread = watch("opencode-", 70, stop)
        with mock_model.MockModel() as model:
            cfg = {"provider": {"anthropic": {"options": {"baseURL": model.url + "/v1", "apiKey": "sk-x"}}},
                   "model": "anthropic/claude-sonnet-4-5", "permission": {"bash": "allow"}, "autoupdate": False}
            env.update({"XDG_CONFIG_HOME": str(home / ".config"), "XDG_DATA_HOME": str(home / ".local/share"),
                        "XDG_CACHE_HOME": str(home / ".cache"), "XDG_STATE_HOME": str(home / ".local/state"),
                        "OPENCODE_CONFIG_CONTENT": json.dumps(cfg)})
            try:
                subprocess.run([str(opencode), "run", "USE_TOOL please"], cwd=home / "project-e2e", env=env, stdin=subprocess.DEVNULL,
                               capture_output=True, timeout=70)
            except subprocess.TimeoutExpired:
                pass
        time.sleep(2.5)
        stop.set()
        thread.join()
        clear_agents("opencode-")
        states = [s[0] for s in seen]
        # «думає» лампа отримує теж, але імітація моделі відповідає за пів секунди, і спостерігач не завжди його застає
        assert ("busy", "bash") in seen and states[-1] == "done" and states.index("busy") < states.index("done"), seen
        return sh(f"{opencode} --version").stdout.strip()

# ------------------------------------------------------------------------------------------------ MCP
if wanted("mcp"):
    section = "MCP"

    def rpc(method, params=None, rid=1):
        return call("/mcp", {"jsonrpc": "2.0", "id": rid, "method": method, "params": params or {}})

    @check("знайомство, перелік інструментів, ping")
    def _():
        init = rpc("initialize", {"protocolVersion": "2025-03-26"})["result"]
        assert init["serverInfo"] == {"name": "agentlight", "version": debug()["device"]["version"]}
        assert [t["name"] for t in rpc("tools/list")["result"]["tools"]] == ["set_status", "get_status"]
        assert rpc("ping")["result"] == {}

    @check("set_status міняє стан, get_status його повертає")
    def _():
        result = rpc("tools/call", {"name": "set_status", "arguments": {"state": "waiting", "agent_id": "e2e-mcp", "name": "mcp"}})["result"]
        assert not result["isError"] and agent("e2e-mcp")["state"] == "waiting"
        text = json.loads(rpc("tools/call", {"name": "get_status", "arguments": {}})["result"]["content"][0]["text"])
        assert text["state"] == "waiting" and "signal" in text and "wifi" not in text
        call("/api/status", {"state": "idle", "agent_id": "e2e-mcp"})

    @check("помилки: невідомий інструмент, метод, зіпсований запит, сповіщення")
    def _():
        assert rpc("tools/call", {"name": "nope"})["result"]["isError"]
        assert rpc("tools/call", {"name": "set_status", "arguments": {"state": "zzz"}})["result"]["isError"]
        assert rpc("nope")["error"]["code"] == -32601
        assert call("/mcp", b"{broken", raw=True)[0] == 400
        assert call("/mcp", {"jsonrpc": "2.0", "method": "notifications/initialized"}, raw=True) == (202, b"")
        assert call("/mcp", raw=True, method="GET")[0] == 405

    @check("справжній Claude Code підключається до лампи як до MCP-сервера й викликає інструмент")
    def _():
        claude = work / "cli" / "node_modules" / ".bin" / "claude"
        if not claude.exists():
            raise Skip("розділ cli не запускався")
        home = work / "mcp-home"
        (home / "p").mkdir(parents=True)
        env = {"PATH": os.environ["PATH"], "HOME": str(home), "CLAUDE_CONFIG_DIR": str(home / ".claude"), "DISABLE_TELEMETRY": "1",
               "DISABLE_AUTOUPDATER": "1", "CLAUDE_CODE_DISABLE_NONESSENTIAL_TRAFFIC": "1"}
        added = subprocess.run([str(claude), "mcp", "add", "--transport", "http", "agentlight", LAMP + "/mcp"], cwd=home / "p", env=env,
                               capture_output=True, text=True, timeout=60)
        assert added.returncode == 0, added.stderr
        listed = subprocess.run([str(claude), "mcp", "list"], cwd=home / "p", env=env, capture_output=True, text=True, timeout=60).stdout
        assert "Connected" in listed, listed
        mock_model.TOOL_NAME = "mcp__agentlight__set_status"
        mock_model.TOOL_INPUT = {"state": "waiting", "agent_id": "e2e-mcp-claude", "name": "через MCP", "message": "виклик із Claude Code"}
        with mock_model.MockModel() as model:
            env.update({"ANTHROPIC_API_KEY": "sk-ant-not-real", "ANTHROPIC_BASE_URL": model.url})
            subprocess.run([str(claude), "-p", "--dangerously-skip-permissions", "USE_TOOL please"], cwd=home / "p", env=env,
                           stdin=subprocess.DEVNULL, capture_output=True, timeout=90)
        a = agent("e2e-mcp-claude")
        assert a and (a["state"], a["name"], a["message"]) == ("waiting", "через MCP", "виклик із Claude Code"), a
        call("/api/status", {"state": "idle", "agent_id": "e2e-mcp-claude"})

# ------------------------------------------------------------------------------------------------ режими й таймери
if wanted("modes"):
    section = "Режими й таймери"
    action("clear")

    @check("перемикання між п'ятьма режимами")
    def _():
        for mode in ("lamp", "focus", "games", "music", "agents"):
            assert config({"mode": mode})["mode"] == mode
        assert config({"mode": "disco"})["mode"] == "agents"
        return "агенти, лампа, фокус, ігри, музика"

    @check("вимкнути й увімкнути світло")
    def _():
        assert action("off")["off"] is True and action("toggle")["off"] is False and action("off")["off"] is True
        assert action("on")["off"] is False

    @check("дії доступні лише у своєму режимі")
    def _():
        config({"mode": "agents"})
        for name in ("sleep", "focus_toggle", "animation"):
            assert call("/api/action", {"action": name}, raw=True)[0] == 400, name
        assert call("/api/action", {"action": "bogus"}, raw=True)[0] == 400
        wrong = config({"touch": {"lamp": {"tap": "dismiss"}, "agents": {"hold": "sleep"}}})["settings"]["touch"]
        assert wrong["lamp"]["tap"] == saved["touch"]["lamp"]["tap"] and wrong["agents"]["hold"] == saved["touch"]["agents"]["hold"]

    @check("кожну дію сенсора можна призначити у своєму режимі")
    def _():
        d = debug()
        for mode, actions in d["actions"].items():
            if mode == "games":
                continue
            for name in actions:
                got = config({"touch": {mode: {"double": name}}})["settings"]["touch"][mode]["double"]
                assert got == name, (mode, name, got)
        config({"touch": saved["touch"]})
        return ", ".join(f"{m}: {len(a)}" for m, a in d["actions"].items() if m != "games")

    @check("колір і анімація кожного стану; проба на лампі")
    def _():
        d = debug()
        for name in d["animations"]:
            assert config({"anims": {"waiting": name}})["settings"]["anims"]["waiting"] == name
        assert config({"anims": {"waiting": "nope"}})["settings"]["anims"]["waiting"] == d["animations"][-1]
        assert config({"colors": {"busy": "#123456", "idle": "#000102"}})["settings"]["colors"]["busy"] == "#123456"
        assert config({"colors": {"busy": "red"}})["settings"]["colors"]["busy"] == "#123456"
        for state in ("busy", "waiting", "done", "error", "idle"):
            assert call("/api/action", {"action": "preview", "state": state}, raw=True)[0] == 200
        assert call("/api/action", {"action": "preview", "state": "zzz"}, raw=True)[0] == 400
        config({"colors": saved["colors"], "anims": saved["anims"]})
        return f"{len(d['animations'])} анімацій"

    @check("межі: яскравість, кількість діодів, тривалості")
    def _():
        s = config({"brightness": 9999, "leds": 99, "ttl_done": 99999, "sleep_min": 0, "focus": {"work_min": 0, "break_min": 999}})["settings"]
        assert (s["brightness"], s["leds"], s["ttl_done"], s["sleep_min"], s["focus"]["work_min"], s["focus"]["break_min"]) == (255, 10, 1440, 1, 1, 60), s
        assert config({"brightness": 1})["settings"]["brightness"] == 5
        config({k: saved[k] for k in ("brightness", "leds", "ttl_done", "sleep_min", "focus")})

    @check("три таймери разом: «готово» гасне, фокус переходить у перерву, лампа вимикається")
    def _():
        config({"ttl_done": 1, "focus": {"work_min": 1, "break_min": 1}, "lamp": {"off_min": 1}, "mode": "focus"})
        action("focus_reset")
        call("/api/status", {"state": "done", "agent_id": "e2e-ttl"})
        started = action("focus_toggle")["focus"]
        assert (started["phase"], started["left"]) == ("work", 60), started
        time.sleep(4)
        action("focus_toggle")
        paused = status()["focus"]
        time.sleep(3)
        assert status()["focus"]["left"] == paused["left"] and paused["paused"], "на паузі час не має йти"
        action("focus_toggle")
        lamp = config({"mode": "lamp"})
        assert 55 <= lamp["lamp_left"] <= 60, lamp["lamp_left"]
        time.sleep(63)
        s = status()
        assert agent("e2e-ttl") is None, "«готово» мало згаснути за хвилину"
        assert (s["focus"]["phase"], s["focus"]["cycles"]) == ("break", 1), s["focus"]
        assert s["off"] is True and s["lamp_left"] == 0, "лампа мала вимкнутись за хвилину"
        skipped = action("on") and config({"mode": "focus"}) and action("focus_skip")["focus"]
        assert skipped["phase"] == "work" and skipped["cycles"] == 1
        assert action("focus_reset")["focus"] == {"phase": "idle", "paused": False, "left": 0, "total": 0, "cycles": 0}

    @check("таймер сну плавно доводить до вимкнення")
    def _():
        config({"mode": "lamp", "sleep_min": 1, "lamp": {"off_min": 0}})
        assert action("sleep")["sleep_left"] == 60
        time.sleep(30)
        middle = status()
        assert 25 <= middle["sleep_left"] <= 32 and not middle["off"], middle["sleep_left"]
        time.sleep(33)
        assert status()["off"] is True
        assert action("on")["sleep_left"] == 0, "увімкнення світла скасовує таймер"

    @check("ігри: марафон, кубик, реакція, фальстарт, 10 секунд, рекорди")
    def _():
        config({"mode": "games", "game": 4})
        action("game_records")
        for _ in range(7):
            action("game_tap")
        time.sleep(11)
        p = status()["play"]
        assert (p["stage"], p["last"][4], p["best"][4]) == ("result", 7, 7), p
        config({"game": 5, "dice": 1})
        action("game_tap")
        time.sleep(2)
        assert 1 <= status()["play"]["last"][5] <= saved["leds"]
        config({"game": 0})
        action("game_tap")
        assert status()["play"]["stage"] == "wait"
        for _ in range(60):
            if status()["play"]["stage"] == "go":
                break
            time.sleep(0.15)
        action("game_tap")
        reaction = status()["play"]
        assert reaction["stage"] == "result" and 0 < reaction["last"][0] < 1500, reaction
        time.sleep(4)
        action("game_tap")
        action("game_tap")
        assert status()["play"]["stage"] == "fail", "дотик на червоне — фальстарт"
        config({"game": 2})
        action("game_tap")
        time.sleep(10)
        action("game_tap")
        ten = status()["play"]
        assert ten["stage"] == "result" and ten["last"][2] < 1500, ten
        assert action("game_records")["play"]["best"] == [0, 0, 0, 0, 0, 0]
        return f"реакція через мережу {reaction['last'][0]} мс, «10 секунд» — помилка {ten['last'][2]} мс"

    @check("сигнал агентові видно в стані й через MCP")
    def _():
        config({"mode": "agents"})
        before = status()["signal"]["count"]
        assert action("signal")["signal"]["count"] == before + 1
        text = json.loads(call("/mcp", {"jsonrpc": "2.0", "id": 1, "method": "tools/call", "params": {"name": "get_status", "arguments": {}}})["result"]["content"][0]["text"])
        assert text["signal"]["count"] == before + 1 and text["signal"]["ago"] < 5

    @check("запит на адресу доходить до сервера")
    def _():
        import http.server
        got = []

        class Handler(http.server.BaseHTTPRequestHandler):
            def log_message(self, *a):
                pass

            def do_POST(self):
                got.append((self.path, json.loads(self.rfile.read(int(self.headers["Content-Length"])))))
                self.send_response(200)
                self.end_headers()
        server = http.server.HTTPServer(("0.0.0.0", 0), Handler)
        threading.Thread(target=server.serve_forever, daemon=True).start()
        me = sh("ipconfig getifaddr en0 || hostname -I | cut -d' ' -f1").stdout.strip()
        config({"webhook": f"http://{me}:{server.server_address[1]}/hook/e2e?x=1"})
        action("webhook")
        time.sleep(1.5)
        server.shutdown()
        config({"webhook": saved["webhook"]})
        assert got and got[0][0] == "/hook/e2e?x=1" and got[0][1]["gesture"] == "page" and got[0][1]["mode"] == "agents", got
        return json.dumps(got[0][1], ensure_ascii=False)

    @check("пульт: лампа спарована з цим Mac і її клавіша гучності справді міняє гучність")
    def _():
        remote = config({"mode": "music"})["remote"]
        config({"mode": "agents"})
        if not remote["connected"]:
            for name in ("volume_up", "key_f13"):
                assert call("/api/action", {"action": name}, raw=True)[0] == 200    # без пристрою дії просто нічого не роблять
            raise Skip(f"жоден пристрій не підключений до лампи як до пульта (спаровано: {remote['bonds']})")
        volume = lambda: int(sh("osascript -e 'output volume of (get volume settings)'").stdout.strip())  # noqa: E731
        before = volume()
        sh(f"osascript -e 'set volume output volume {min(before, 60)}'")
        start = volume()
        action("volume_up")
        time.sleep(1)
        up = volume()
        action("volume_down")
        action("volume_down")
        time.sleep(1)
        down = volume()
        sh(f"osascript -e 'set volume output volume {before}'")
        if (start, up, down) == (start, start, start) and len(remote["devices"]) > 1:
            raise Skip("активний зараз інший пристрій, не цей Mac; хто отримує клавіші, перевіряє наступна перевірка")
        assert up > start and down < up, (start, up, down)
        return f"гучність {start} → {up} → {down}, потім повернув {before}"

    @check("пульт: клавіші йдуть лише вибраному пристрою")
    def _():
        devices = status()["remote"]["devices"]
        if len(devices) < 2 or not all(d["connected"] for d in devices[:2]):
            raise Skip("потрібні два підключені спаровані пристрої")
        volume = lambda: int(sh("osascript -e 'output volume of (get volume settings)'").stdout.strip())  # noqa: E731
        original = next(d["id"] for d in devices if d["active"])
        before = volume()
        sh("osascript -e 'set volume output volume 40'")
        moved = {}
        for d in devices[:2]:
            assert [x["id"] for x in config({"remote": {"active": d["id"]}})["remote"]["devices"] if x["active"]] == [d["id"]]
            start = volume()
            action("volume_up")
            time.sleep(1)
            moved[d["id"]] = volume() != start
            action("volume_down")
            time.sleep(1)
        assert [x["id"] for x in config({"remote": {"active": "11:22:33:44:55:66"}})["remote"]["devices"] if x["active"]] == [devices[1]["id"]]
        config({"remote": {"active": original}})
        sh(f"osascript -e 'set volume output volume {before}'")
        assert sorted(moved.values()) == [False, True], moved      # гучність цього Mac міняє рівно один із двох
        return "гучність цього Mac змінилась лише тоді, коли активним був він"

    @check("налаштування переживають перезавантаження; «типові» їх скидає")
    def _():
        config({"mode": "lamp", "lamp": {"color": "#00d0ff", "anim": "wave", "off_min": 0}, "focus": {"work_min": 33}, "game": 3,
                "touch": {"music": {"hold": "key_f15"}}, "brightness": 77})
        call("/api/action", {"action": "reboot"}, raw=True)
        time.sleep(6)
        wait_online()
        d = debug()
        s = d["settings"]
        assert (d["mode"], s["lamp"]["color"], s["lamp"]["anim"], s["focus"]["work_min"], d["play"]["game"], s["touch"]["music"]["hold"], s["brightness"]) \
            == ("lamp", "#00d0ff", "wave", 33, 3, "key_f15", 77), s
        assert d["device"]["uptime"] < 60 and d["agents"] == []
        after = action("defaults")["settings"]
        assert (after["lamp"]["color"], after["focus"]["work_min"], after["touch"]["music"]["hold"]) == ("#ffb060", 25, "media_prev")

    config({k: saved[k] for k in ("brightness", "leds", "ttl_busy", "ttl_done", "ttl_attention", "colors", "anims", "lamp", "sleep_min", "focus", "webhook", "touch")})
    config({"mode": saved_mode, "game": 0, "dice": 0})

# ------------------------------------------------------------------------------------------------ WiFi й Bluetooth
if wanted("radio"):
    section = "WiFi і Bluetooth"

    @check("лампа бачить мережі довкола, зокрема свою")
    def _():
        found = call("/api/scan", timeout=20)
        assert status()["wifi"]["ssid"] in [n["ssid"] for n in found], found
        return f"мереж: {len(found)}, сигнал своєї {status()['wifi']['rssi']} dBm"

    try:
        import asyncio
        from bleak import BleakClient, BleakScanner
        have_ble = True
    except ImportError:
        have_ble = False
    SERVICE = "a9e10001-7c1e-4b6f-9d2a-41676e744c69"
    char = lambda n: f"a9e1000{n}-7c1e-4b6f-9d2a-41676e744c69"  # noqa: E731

    async def find():
        found = {}

        def seen(device, adv):
            if SERVICE in adv.service_uuids:
                found[device.address] = (device, adv)
        for _ in range(4):
            async with BleakScanner(seen):
                await asyncio.sleep(6)
            if found:
                return list(found.values())[0]
        raise AssertionError("лампу не видно по Bluetooth")

    async def ble_status(device):
        async with BleakClient(device) as client:
            return json.loads((await client.read_gatt_char(char(2))).decode())

    async def ble_cmd(device, payload):
        async with BleakClient(device) as client:
            await client.write_gatt_char(char(4), json.dumps(payload).encode(), response=True)

    @check("Bluetooth: лампа оголошує налаштування WiFi і клавіатуру")
    def _():
        if not have_ble:
            raise Skip("немає bleak")
        device, adv = asyncio.run(find())
        assert "00001812-0000-1000-8000-00805f9b34fb" in adv.service_uuids and adv.local_name == status()["wifi"]["ap"]
        return f"{adv.local_name}, сигнал {adv.rssi} dBm"

    @check("Bluetooth: стан і пошук мереж")
    def _():
        if not have_ble:
            raise Skip("немає bleak")

        async def run():
            device, _ = await find()
            async with BleakClient(device) as client:
                state = json.loads((await client.read_gatt_char(char(2))).decode())
                before = json.loads((await client.read_gatt_char(char(3))).decode())["seq"]
                await client.write_gatt_char(char(4), json.dumps({"cmd": "scan"}).encode(), response=True)
                for _ in range(15):
                    await asyncio.sleep(1)
                    scan = json.loads((await client.read_gatt_char(char(3))).decode())
                    if scan["seq"] != before:
                        return state, scan
            raise AssertionError("пошук мереж не відповів")
        state, scan = asyncio.run(run())
        assert state["ip"] == args.lamp and state["ssid"] in scan["list"]
        return f"мереж: {len(scan['list'])}"

    @check("Bluetooth: додати мережу, вибрати з двох ту, що поруч, забути")
    def _():
        if not have_ble:
            raise Skip("немає bleak")
        home_net = status()["wifi"]["ssid"]
        fake = "AgentLight-E2E-Net"

        async def run():
            device, _ = await find()
            await ble_cmd(device, {"cmd": "add", "ssid": fake, "pass": "пароль із пробілами 123"})
            await asyncio.sleep(14)
            device, _ = await find()
            added = await ble_status(device)
            await ble_cmd(device, {"cmd": "forget", "ssid": fake})
            await asyncio.sleep(14)
            device, _ = await find()
            return added, await ble_status(device)
        added, after = asyncio.run(run())
        wait_online()
        assert added["saved"][0] == fake and home_net in added["saved"] and added["ssid"] == home_net, added
        assert fake not in after["saved"] and after["ssid"] == home_net, after
        return f"із двох збережених підключилась до {home_net}"

# ------------------------------------------------------------------------------------------------ оновлення
if wanted("ota"):
    section = "Оновлення прошивки"
    BIN = FIRMWARE / ".pio" / "build" / "c3_supermini" / "firmware.bin"

    def upload(path, headers):
        boundary = "e2eboundary"
        body = (f"--{boundary}\r\nContent-Disposition: form-data; name=\"firmware\"; filename=\"firmware.bin\"\r\n"
                "Content-Type: application/octet-stream\r\n\r\n").encode() + pathlib.Path(path).read_bytes() + f"\r\n--{boundary}--\r\n".encode()
        code, content = call("/api/update", body, raw=True, timeout=120,
                             headers={"Content-Type": f"multipart/form-data; boundary={boundary}", **headers})
        return json.loads(content or b"{}")

    def sign(path, key=KEY):
        return base64.b64encode(subprocess.run(["openssl", "dgst", "-sha256", "-sign", str(key), str(path)], check=True, capture_output=True).stdout).decode()

    def build(flag):
        result = sh(f"cd {FIRMWARE} && PLATFORMIO_BUILD_FLAGS='-DE2E_BUILD={flag}' pio run -e c3_supermini", timeout=600)
        assert result.returncode == 0, result.stdout[-400:]
        return next(line for line in sh(f"strings {BIN}").stdout.splitlines() if " 2026 " in line and line.count(":") == 2)

    OTA_PASSWORD = "e2e-check-password"      # сталий: якщо перевірка впаде посередині, його можна зняти вручну
    can = KEY.exists() and shutil.which("pio")
    bench = call("/api/allow/touch?yes=0", b"", raw=True)[0] != 404

    @check("опублікована прошивка: файл, розмір, хеш і підпис сходяться з ключем у репозиторії")
    def _():
        manifest = json.loads(urllib.request.urlopen(PAGES + "firmware/latest.json", timeout=30).read())
        data = urllib.request.urlopen(PAGES + "firmware/" + manifest["file"], timeout=60).read()
        (work / "release.bin").write_bytes(data)
        (work / "release.sig").write_bytes(base64.b64decode(manifest["signature"]))
        assert len(data) == manifest["size"] and hashlib.sha256(data).hexdigest() == manifest["sha256"]
        verified = sh(f"openssl dgst -sha256 -verify {FIRMWARE / 'update_public_key.pem'} -signature {work / 'release.sig'} {work / 'release.bin'}")
        assert verified.returncode == 0, verified.stdout + verified.stderr
        source = sh(f"sed -n 's/#define FW_VERSION \"\\(.*\\)\"/\\1/p' {FIRMWARE / 'src' / 'app.h'}").stdout.strip()
        assert manifest["version"] == source, f"опубліковано {manifest['version']}, у коді {source}"
        return f"версія {manifest['version']}, {len(data) // 1024} КБ"

    @check("лампа відхиляє: без підпису й пароля, сміття, обрізаний файл, змінений байт, чужий ключ")
    def _():
        if not can:
            raise Skip("немає ключа підпису або PlatformIO")
        if not BIN.exists():
            build("0")
        before = debug()["device"]["build"]
        good = sign(BIN)
        junk = work / "junk.bin"
        junk.write_bytes(os.urandom(200000))
        half = work / "half.bin"
        half.write_bytes(BIN.read_bytes()[:400000])
        tampered = work / "tampered.bin"
        data = bytearray(BIN.read_bytes())
        data[200000] ^= 0x55
        tampered.write_bytes(data)
        other = work / "other.pem"
        subprocess.run(["openssl", "ecparam", "-name", "prime256v1", "-genkey", "-noout", "-out", str(other)], check=True, capture_output=True)
        answers = {
            "без підпису й пароля": upload(BIN, {}),
            "сміття з підписом": upload(junk, {"X-Signature": sign(junk)}),
            "обрізаний файл": upload(half, {"X-Signature": sign(half)}),
            "змінений байт": upload(tampered, {"X-Signature": good}),
            "чужий ключ": upload(BIN, {"X-Signature": sign(BIN, other)}),
            "підпис-сміття": upload(BIN, {"X-Signature": "!!!"}),
        }
        assert all("error" in a for a in answers.values()), answers
        d = debug()
        assert d["device"]["build"] == before and d["device"]["uptime"] > 20, "лампа мала лишитись на старій прошивці без перезавантаження"
        return "; ".join(f"{k} → {v['error']}" for k, v in answers.items())

    @check("підписана збірка ставиться без пароля, і запускається саме вона")
    def _():
        if not can:
            raise Skip("немає ключа підпису або PlatformIO")
        stamp = build("1")
        assert upload(BIN, {"X-Signature": sign(BIN)}) == {"ok": True}
        time.sleep(8)
        wait_online()
        assert debug()["device"]["build"] == stamp, (debug()["device"]["build"], stamp)
        return f"збірка {stamp}"

    @check("свій файл із паролем: задати, невірний, залити, зняти")
    def _():
        if not can:
            raise Skip("немає ключа підпису або PlatformIO")
        password = OTA_PASSWORD
        assert call("/api/ota/password", {"new": "abc"})["error"] == "password too short"
        assert call("/api/ota/password", {"new": password}) == {"ok": True}
        assert call("/api/ota/password", {"new": "another-pass"})["error"] == "wrong password"
        stamp = build("2")
        assert upload(BIN, {"X-OTA-Password": "wrong"})["error"] == "wrong password"
        assert upload(BIN, {"X-OTA-Password": password}) == {"ok": True}
        time.sleep(8)
        wait_online()
        assert debug()["device"]["build"] == stamp and debug()["device"]["ota_ready"] is True
        globals()["ota_password"] = password
        return f"збірка {stamp}"

    @check("оновлення з PlatformIO по WiFi; невірний пароль відхиляється")
    def _():
        if "ota_password" not in globals():
            raise Skip("попередня перевірка не пройшла")
        wrong = sh(f"cd {FIRMWARE} && AGENTLIGHT_OTA_PASSWORD=wrong pio run -e ota -t upload --upload-port {args.lamp}", timeout=600)
        assert "Authentication Failed" in wrong.stdout + wrong.stderr
        for attempt in (1, 2):                 # одразу після відхиленої спроби лампа інколи ще не готова прийняти нову
            good = sh(f"cd {FIRMWARE} && PLATFORMIO_BUILD_FLAGS='-DE2E_BUILD=3' AGENTLIGHT_OTA_PASSWORD={ota_password} pio run -e ota -t upload --upload-port {args.lamp}", timeout=600)  # noqa: F821
            if "Result: OK" in good.stdout + good.stderr:
                break
            time.sleep(10)
            wait_online()
        assert "Result: OK" in good.stdout + good.stderr, (good.stdout + good.stderr)[-300:]
        time.sleep(8)
        wait_online()
        stamp = next(line for line in sh(f"strings {FIRMWARE / '.pio/build/ota/firmware.bin'}").stdout.splitlines() if " 2026 " in line and line.count(":") == 2)
        assert debug()["device"]["build"] == stamp
        assert call("/api/ota/password", {"old": ota_password, "new": ""}) == {"ok": True} and debug()["device"]["ota_ready"] is False  # noqa: F821
        return f"збірка {stamp}" + (" (з другої спроби)" if attempt == 2 else "")

    @check("пароль перевірки знято з лампи")
    def _():
        call("/api/ota/password", {"old": OTA_PASSWORD, "new": ""})
        assert debug()["device"]["ota_ready"] is False, "на лампі лишився пароль оновлення"

    @check("наприкінці на лампі — опублікована прошивка з GitHub")
    def _():
        if bench:
            raise Skip("на лампі перевірна збірка: офіційну поставлю після розділу allow")
        if not (work / "release.bin").exists():
            raise Skip("опубліковану прошивку не завантажено")
        manifest = json.loads(urllib.request.urlopen(PAGES + "firmware/latest.json", timeout=30).read())
        assert upload(work / "release.bin", {"X-Signature": manifest["signature"]}) == {"ok": True}
        time.sleep(8)
        wait_online()
        d = debug()
        assert d["device"]["version"] == manifest["version"] and call("/api/allow/touch?yes=1", b"", raw=True)[0] == 404
        return f"версія {d['device']['version']}, зібрана {d['device']['build']}"

# ------------------------------------------------------------------------------------------------ дозволити
if wanted("allow"):
    section = "Дозволити (експериментально)"
    bench = call("/api/allow/touch?yes=0", b"", raw=True)[0] != 404
    home = work / "allow-home"
    home.mkdir()
    env = dict(os.environ, HOME=str(home), AGENTLIGHT_HOST=args.lamp)
    call("/api/allow/forget", {})
    config({"allow": {"enabled": False, "edits": True, "commands": True, "other": False}})

    def touch_later(seconds, yes):
        thread = threading.Thread(target=lambda: (time.sleep(seconds), call(f"/api/allow/touch?yes={yes}", b"", raw=True)), daemon=True)
        thread.start()
        return thread

    def hook(tool, command, extra=None):
        event = {"session_id": "e2eallow-1", "cwd": "/tmp/e2e-allow", "hook_event_name": "PermissionRequest", "tool_name": tool,
                 "tool_input": {("file_path" if tool in ("Edit", "Write") else "command"): command, **(extra or {})}}
        started = time.time()
        out = subprocess.run([str(home / ".agentlight" / "allow.sh"), "claude"], input=json.dumps(event), env=env, capture_output=True, text=True, timeout=40)
        return out.stdout.strip(), time.time() - started

    def decision(text):
        return json.loads(text)["hookSpecificOutput"]["decision"]["behavior"] if text else None

    @check("у звичайній збірці «торкнутись» лампи запитом не можна")
    def _():
        if bench:
            raise Skip("на лампі перевірна збірка")
        assert call("/api/allow/touch?yes=1", b"", raw=True)[0] == 404

    @check("спарювання без дотику не відбувається")
    def _():
        started = call("/api/allow/pair", {"key": "e2e00001", "secret": "0" * 32, "name": "e2e"})
        assert started == {"pairing": True} and status()["allow"]["pairing"] == "e2e"
        assert call("/api/allow/pair", {"key": "e2e00002", "secret": "1" * 32, "name": "second"}) == {"refused": "busy"}
        assert call("/api/allow/pair", {"key": "short", "secret": "x"}) == {"refused": "bad key"}
        time.sleep(32)
        assert call("/api/allow/pair?key=e2e00001")["state"] == "expired" and status()["allow"]["computers"] == []
        nonce = os.urandom(8).hex()
        assert call("/api/allow/ask", {"key": "e2e00001", "nonce": nonce, "agent_id": "x", "name": "x", "tool": "bash", "detail": "ls"})["refused"] in ("disabled", "not paired")
        return "30 секунд без дотику — лампа комп'ютер не запам'ятала"

    @check("спарювання встановлювачем і дотиком")
    def _():
        if not bench:
            raise Skip("потрібен дотик: лише на перевірній збірці")
        waiter = touch_later(3, 1)
        result = sh(f"curl -4 -fsS {LAMP}/install.sh | sh -s -- claude allow", env=env, timeout=90)
        waiter.join()
        assert result.returncode == 0, result.stderr
        conf = dict(line.split("=", 1) for line in (home / ".agentlight" / "allow.conf").read_text().split())
        assert len(conf["SECRET"]) == 32 and (home / ".agentlight" / "allow.conf").stat().st_mode & 0o077 == 0
        assert len(status()["allow"]["computers"]) == 1
        return f"лампа запам'ятала «{status()['allow']['computers'][0]}»"

    @check("відхилене спарювання нічого не лишає")
    def _():
        if not bench:
            raise Skip("потрібен дотик: лише на перевірній збірці")
        other = work / "allow-rejected"
        other.mkdir()
        waiter = touch_later(3, 0)
        result = sh(f"curl -4 -fsS {LAMP}/install.sh | sh -s -- claude allow", env=dict(env, HOME=str(other)), timeout=90)
        waiter.join()
        assert result.returncode != 0 and not (other / ".agentlight" / "allow.conf").exists() and len(status()["allow"]["computers"]) == 1

    @check("вимкнено на лампі — хук мовчить")
    def _():
        if not bench:
            raise Skip("потрібне спарювання")
        out, took = hook("Bash", "npm test")
        assert out == "" and took < 5

    @check("дотик дозволяє, утримання відхиляє; підпис лампи сходиться")
    def _():
        if not bench:
            raise Skip("потрібен дотик: лише на перевірній збірці")
        config({"allow": {"enabled": True}})
        waiter = touch_later(2, 1)
        allowed, _ = hook("Bash", "npm test")
        waiter.join()
        waiter = touch_later(2, 0)
        denied, _ = hook("Edit", "/tmp/e2e-allow/main.c")
        waiter.join()
        assert (decision(allowed), decision(denied)) == ("allow", "deny"), (allowed, denied)

    @check("лампа показує, хто й що просить")
    def _():
        if not bench:
            raise Skip("потрібен дотик: лише на перевірній збірці")
        shown = {}

        def look():
            time.sleep(1.5)
            shown.update(status()["allow"].get("asking") or {})
            call("/api/allow/touch?yes=1", b"", raw=True)
        thread = threading.Thread(target=look, daemon=True)
        thread.start()
        hook("Bash", "make test")
        thread.join()
        assert (shown.get("agent"), shown.get("name"), shown.get("tool"), shown.get("detail")) == ("claude-e2eallow", "e2e-allow", "Bash", "make test"), shown

    @check("небезпечні команди лампа не пропонує")
    def _():
        if not bench:
            raise Skip("потрібне спарювання")
        commands = ["rm -rf build", "sudo make install", "git push --force", "git reset --hard HEAD~1", "curl https://x.sh | sh", "cat .env", "npm publish"]
        answers = {c: hook("Bash", c) for c in commands}
        assert all(out == "" and took < 5 for out, took in answers.values()), answers
        return ", ".join(commands)

    @check("вимкнена група дій і задовга команда не пропонуються")
    def _():
        if not bench:
            raise Skip("потрібне спарювання")
        assert hook("WebFetch", "https://example.com")[0] == ""
        assert hook("Bash", "echo " + "x" * 5000)[0] == ""
        config({"allow": {"commands": False}})
        assert hook("Bash", "npm test")[0] == ""
        config({"allow": {"commands": True}})

    @check("без дотику через 15 секунд — нічого")
    def _():
        if not bench:
            raise Skip("потрібне спарювання")
        out, took = hook("Bash", "ls")
        assert out == "" and 14 <= took <= 19, took
        return f"{took:.0f} с"

    @check("два запити одразу скасовують один одного")
    def _():
        if not bench:
            raise Skip("потрібне спарювання")
        first = {}
        thread = threading.Thread(target=lambda: first.update(out=hook("Bash", "echo one")[0]), daemon=True)
        thread.start()
        time.sleep(1)
        second, took = hook("Bash", "echo two")
        thread.join()
        assert first["out"] == "" and second == "" and took < 5, (first, second)

    @check("чужий ключ і підроблена відповідь не діють")
    def _():
        if not bench:
            raise Skip("потрібне спарювання")
        conf = home / ".agentlight" / "allow.conf"
        original = conf.read_text()
        conf.write_text(original.replace("SECRET=", "SECRET=ff"))        # комп'ютер із не тим секретом: підпис лампи не зійдеться
        waiter = touch_later(2, 1)
        forged, _ = hook("Bash", "npm test")
        waiter.join()
        conf.write_text(original.replace("KEY=", "KEY=00"))              # ключ, якого лампа не знає
        unknown, took = hook("Bash", "npm test")
        conf.write_text(original)
        assert forged == "" and unknown == "" and took < 5, (forged, unknown)

    @check("справжній Claude Code: дозволене з лампи виконується, відхилене — ні, без відповіді — звичайний порядок")
    def _():
        claude = work / "cli" / "node_modules" / ".bin" / "claude"
        if not bench or not claude.exists():
            raise Skip("потрібні перевірна збірка й розділ cli")
        project = home / "project"
        project.mkdir()
        outcome = {}
        for label, yes in (("allowed", 1), ("denied", 0), ("ignored", None)):
            mock_model.TOOL_NAME = "Bash"
            mock_model.TOOL_INPUT = {"command": f"touch {label}.txt", "description": "Create a marker file"}

            def answer(yes=yes):
                for _ in range(80):
                    if status()["allow"].get("asking"):
                        if yes is not None:
                            time.sleep(1)
                            call(f"/api/allow/touch?yes={yes}", b"", raw=True)
                        return
                    time.sleep(0.3)
            thread = threading.Thread(target=answer, daemon=True)
            thread.start()
            with mock_model.MockModel() as model:
                cenv = {"PATH": os.environ["PATH"], "HOME": str(home), "CLAUDE_CONFIG_DIR": str(home / ".claude"), "ANTHROPIC_API_KEY": "sk-ant-not-real",
                        "ANTHROPIC_BASE_URL": model.url, "DISABLE_TELEMETRY": "1", "DISABLE_AUTOUPDATER": "1", "CLAUDE_CODE_DISABLE_NONESSENTIAL_TRAFFIC": "1"}
                started = time.time()
                subprocess.run([str(claude), "-p", "--permission-mode", "default", "USE_TOOL please"], cwd=project, env=cenv,
                               stdin=subprocess.DEVNULL, capture_output=True, timeout=90)
                outcome[label] = ((project / f"{label}.txt").exists(), round(time.time() - started))
            thread.join()
        clear_agents("claude-")
        assert [outcome[k][0] for k in ("allowed", "denied", "ignored")] == [True, False, False], outcome
        assert outcome["ignored"][1] >= 15, outcome
        return f"без відповіді Claude Code чекав {outcome['ignored'][1]} с і не виконав"

    @check("«забути всі» знімає спарювання")
    def _():
        call("/api/allow/forget", {})
        config({"allow": {"enabled": saved.get("allow", {}).get("enabled", False)}})
        assert status()["allow"]["computers"] == []
        if bench:
            assert hook("Bash", "npm test")[0] == ""

# ------------------------------------------------------------------------------------------------ сайт і CI
if wanted("site"):
    section = "Сайт і автоматика"

    @check("GitHub Pages: сторінка Bluetooth, превью корпусу, файли до друку")
    def _():
        sizes = {}
        for path in ("web/setup.html", "web/", "case/preview/", "case/stl/plate_black.3mf", "case/stl/diffuser.stl", "firmware/latest.json"):
            sizes[path] = len(urllib.request.urlopen(PAGES + path, timeout=30).read())
        assert urllib.request.urlopen(PAGES + "web/setup.html", timeout=30).read() == (ROOT / "web" / "setup.html").read_bytes()
        return ", ".join(sizes)

    @check("власний сайт віддає сторінку налаштування по HTTPS")
    def _():
        body = sh("curl -fsS -m 30 https://agentlight.onelenyk.dev/").stdout     # через curl: сайт за Cloudflare відхиляє urllib
        assert "navigator.bluetooth" in body and "a9e10001-7c1e-4b6f-9d2a-41676e744c69" in body

    @check("останні запуски CI й релізу зелені")
    def _():
        runs = json.loads(sh("gh run list --limit 12 --json name,conclusion,headBranch,status", timeout=60).stdout)
        latest = {}
        for run in runs:
            latest.setdefault(run["name"], run)
        assert all(r["conclusion"] == "success" for r in latest.values()), {k: v["conclusion"] for k, v in latest.items()}
        return "; ".join(f"{name}: {r['headBranch']}" for name, r in latest.items())

# ------------------------------------------------------------------------------------------------ підсумок
action("clear")
shutil.rmtree(work, ignore_errors=True)
counts = {kind: sum(1 for r in results if r[2] == kind) for kind in ("ok", "FAIL", "skip")}
print(f"\nПройшло {counts['ok']}, не пройшло {counts['FAIL']}, пропущено {counts['skip']}")
if args.json:
    args.json.write_text(json.dumps([dict(zip(("section", "check", "result", "detail"), r)) for r in results], ensure_ascii=False, indent=1))
sys.exit(1 if counts["FAIL"] else 0)
